lambdakb/keyboard-lk56hs/output/pcb/img/lk56hs-pcb-bottom.png

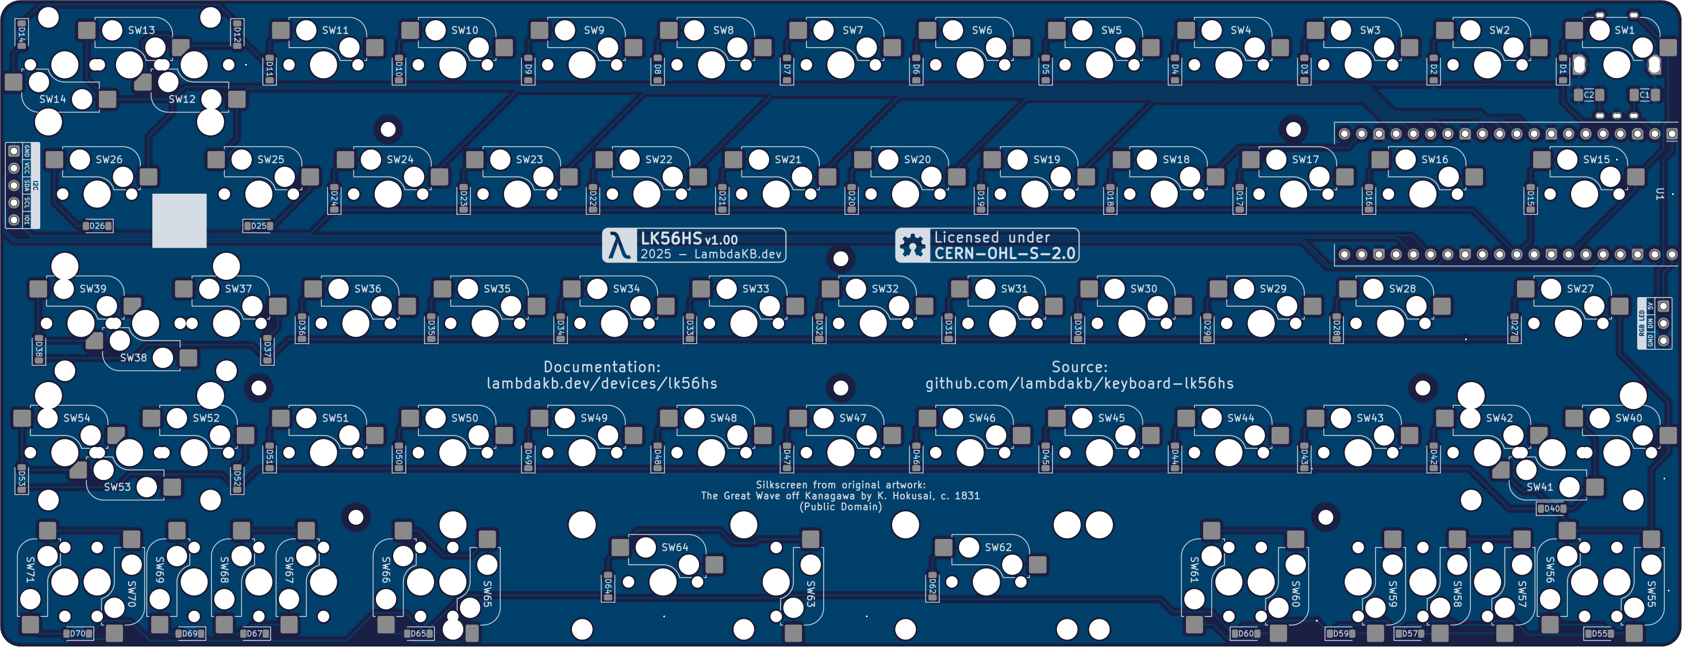
output/pcb/img/lk56hs-pcb-bottom.png
