lambdakb/keyboard-lk56hs/output/pcb/img/lk56hs-pcb-top.png

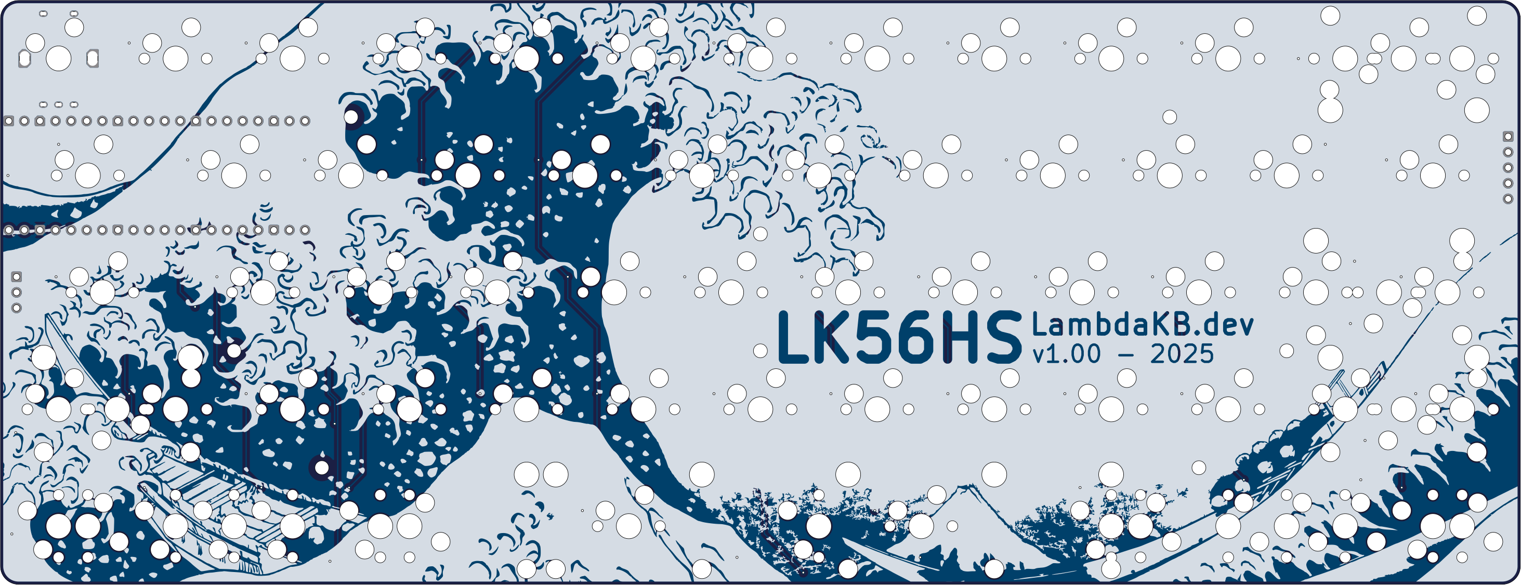
output/pcb/img/lk56hs-pcb-top.png
