lambdakb/keyboard-lk56hs/output/plate/img/lk56hs-plate-bottom.png

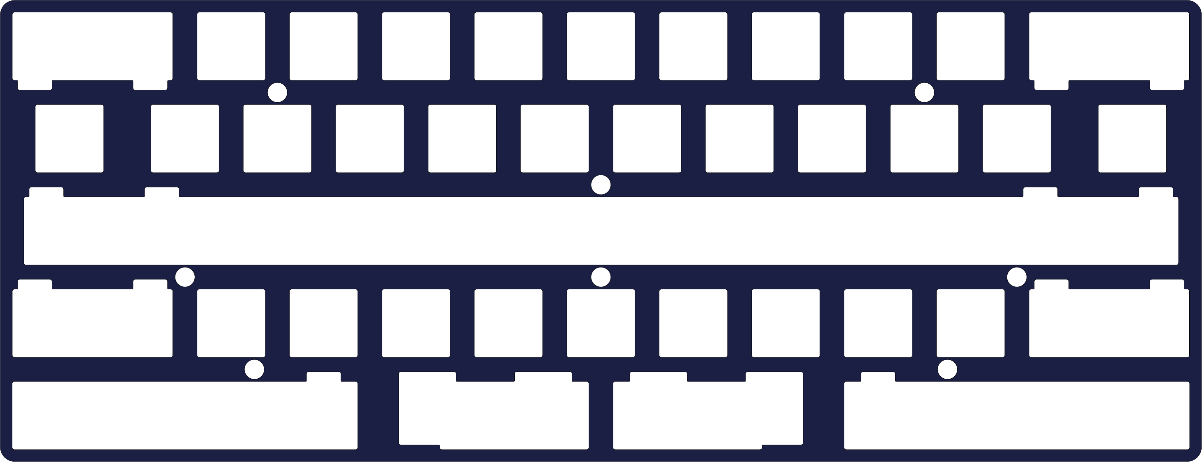
output/plate/img/lk56hs-plate-bottom.png
